jstanley0/astro-timer/firmware/io.c

#include <avr/io.h>
#include <avr/interrupt.h>
#include <avr/sleep.h>
#include <util/delay.h>
#include "io.h"
#include "display.h"
#include "clock.h"

void sysclk_init()
{
    CLKPR = (1 << CLKPCE);
    CLKPR = (1 << CLKPS1); // 1/4 prescaler, for 2MHz operation
}

void io_init()
{
    DDRB  = 0b00111111;
    PORTB = 0b00000000;
    DDRC  = 0b00100000;
    PORTC = 0b00011100;
    DDRD  = 0b11111111;
    PORTD = 0b11111111;
}

// flash the apostrophe. useful for "is this code being reached?"
void blip()
{
    cli();
    DIGITS_OFF();
    DIGIT_VALUE(APOS);
    DIGIT_ON(4);
    _delay_ms(1);
    sei();
}

void power_init()
{
    PRR = (1 << PRTWI) | (1 << PRSPI) | (1 << PRUSART0) | (1 << PRADC);
}

// display "OFF" for a second (or longer)
void acknowledge_power_off()
{
    display[0] = EMPTY;
    display[1] = LETTER_O;
    display[2] = LETTER_F;
    display[3] = LETTER_F;
    display[4] = EMPTY;
    _delay_ms(1000);
    // wait for the button to be released, so the release event doesn't wake us up again
    while(BUTTON_STATE() != 0x7);
}

// go into as deep a sleep as we can manage, waking up on button input
void power_down()
{
    // stop interrupts so things don't change out from underneath us
    cli();

    // shut down all outputs
    DIGITS_OFF();
    SHUTTER_OFF();
    SHUTTER_HALFPRESS_OFF();

    // stop all timers
    uint8_t saved_TCCR2B = TCCR2B;
    TCCR2B = 0;
    uint8_t saved_TCCR1B = TCCR1B;
    TCCR1B = 0;
    uint8_t saved_TCCR0B = TCCR0B;
    TCCR0B = 0;

    // save pin-change interrupt state, and enable the interrupt on button input
    // (not encoder-turning input, because that can easily happen in a camera bag)
    uint8_t saved_PCMSK1 = PCMSK1;
    PCMSK1 = 0b00011100;
    uint8_t saved_PCICR = PCICR;
    PCICR = (1 << PCIE1);

    // re-enable interrupts so we can actually wake up
    sei();

    for(;;) {
        // power down!
        set_sleep_mode(SLEEP_MODE_PWR_DOWN);
        sleep_mode();

        // a pin-change interrupt woke us up.
        // to avoid spurious wakeups in the camera bag, ensure *two* buttons are held for 300ms
        // and snooze for awhile longer to swallow the button release
        uint8_t hc = 0;
        for(uint8_t delay = 0; delay < 15; ++delay) {
            _delay_ms(50);
            uint8_t buttons = (PINC & 0b00011100) >> 2;
            if (buttons != 0b001 && buttons != 0b010 && buttons != 0b100)
                break;
            ++hc;
        }
        if (hc >= 6)
            break;
    }
    // restore prior state
    PCMSK1 = saved_PCMSK1;
    PCICR = saved_PCICR;
    TCCR0B = saved_TCCR0B;
    TCCR1B = saved_TCCR1B;
    TCCR2B = saved_TCCR2B;

    // wait for the crystal to start ticking
    clock_wait_for_xtal();
}
